lanhp-vn/4-Wheel-PID-Line-Following-Robot/main/Motor_Driver.h

#ifndef motorDriver
#define motorDriver

#if (ARDUINO >=100)
  #include "Arduino.h"
#else
  #include "WProgram.h"
#endif

class Motor_Driver {

  public:
    //Constructor
    Motor_Driver(int ENA, int ENB, int IN1, int IN2, int IN3, int IN4);
    //Methods
    void stopCar();
    void forward();
    void backward();
    void turnRight();
    void shiftRight();
    void shiftLeft();
    void turnLeft();
    void turn_90deg(int direction, int delay_90deg);
    void setSpeed(int left_speed, int right_speed);

  private:
    int _ENA;
    int _ENB;
    int _IN1;
    int _IN2;
    int _IN3;
    int _IN4;

};

#endif
